ralsei/self-lace/CAD/Board/selflace.sch

## EAGLE design CAD/Board/selflace.sch (2019-05-23)

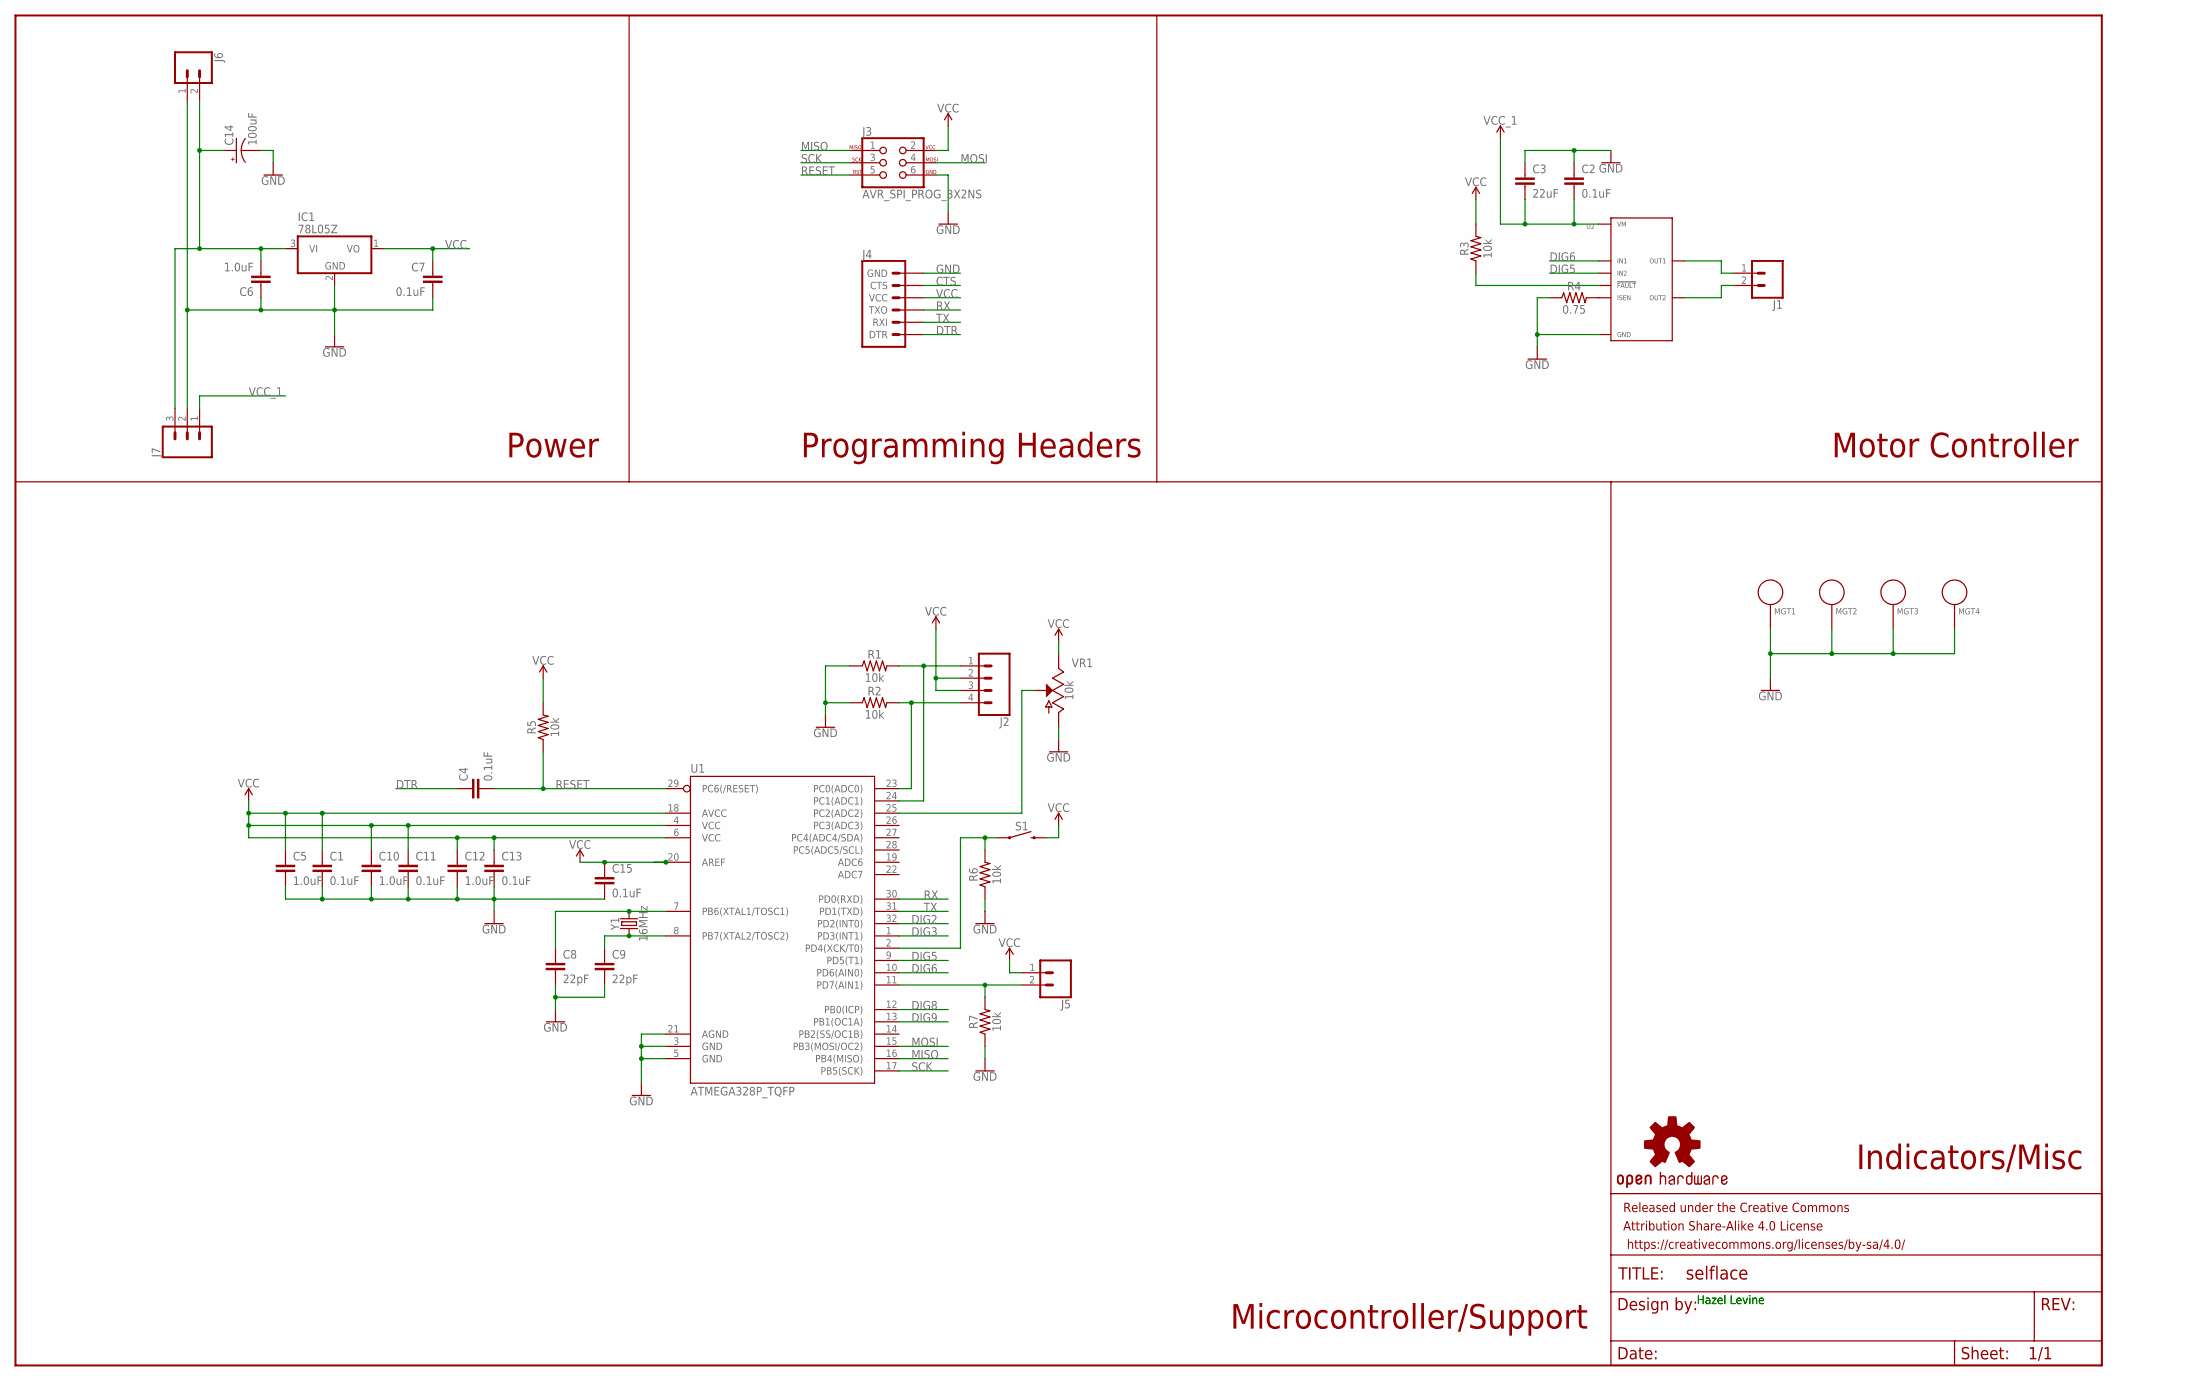
[picture p19: schematic selflace.sch]

Parts:
C1, C2, C4, C7, C11, C13, C15: 0.1uF; 0603
C3: 22uF; 0805
C5, C6, C10, C12: 1.0uF; 0603
C8, C9: 22pF; 0603
C14: 100uF; NIC_10X10.5_CAP
FRAME1: FRAME-LEDGER; CREATIVE_COMMONS
IC1: 78L05Z; TO92
J1, J5: CONN_02; 1X02
J2: CONN_04; 1X04
J3: AVR_SPI_PROG_3X2NS; 2X3-NS
J4: 6_PIN_SERIAL_TARGETSILK; 6_PIN_SERIAL_TARGET_SIDE_W_SILK
J6: CONN_02JST-PTH-2; JST-2-PTH
J7: CONN_03; 1X03
LOGO1: OSHW-LOGOM; OSHW-LOGO-M
MGT1, MGT2, MGT3, MGT4: BEAGLEBONEBLACK_MOUNTING_HOLE
R1, R2, R3, R5, R6, R7: 10k; 0603
R4: 0.75; 0805
S1: MOMENTARY-SWITCH-SPST-PTH-6.0MM; TACTILE_SWITCH_PTH_6.0MM
U1: ATMEGA328P_TQFP; TQFP32-08
U2: DRV8872DDARQ1; DRV8872_HSOP-8
VR1: 10k; POT-PTH-ALPS
Y1: 16MHz; HC49US

Connections:
CTS: J4.P$5 (CTS)
DIG2: U1.32 (PD2(INT0))
DIG3: U1.1 (PD3(INT1))
DIG5: U1.9 (PD5(T1)), U2.P$2 (IN2)
DIG6: U1.10 (PD6(AIN0)), U2.P$3 (IN1)
DIG8: U1.12 (PB0(ICP))
DIG9: U1.13 (PB1(OC1A))
DTR: C4.1, J4.P$1 (DTR)
GND: C1.2, C2.1, C3.1, C5.2, C6.1, C7.2, C8.2, C9.2, C10.2, C11.2, C12.2, C13.2, C14.-, C15.2, IC1.2 (GND), J3.6, J4.P$6 (GND), J6.1, J7.2, MGT1.P$1, MGT2.P$1, MGT3.P$1, MGT4.P$1, R1.1, R2.1, R4.1, R6.1, R7.1, U1.3 (GND), U1.5 (GND), U1.21 (AGND), U2.P$1 (GND), VR1.P$3 (A)
MISO: J3.1, U1.16 (PB4(MISO))
MOSI: J3.4, U1.15 (PB3(MOSI/OC2))
unnamed: R6.2, S1.1, U1.2 (PD4(XCK/T0))
unnamed: J5.2, R7.2, U1.11 (PD7(AIN1))
unnamed: R3.1, U2.P$4 (!FAULT)
unnamed: J1.1, U2.P$6 (OUT1)
unnamed: J1.2, U2.P$8 (OUT2)
unnamed: U1.25 (PC2(ADC2)), VR1.P$2 (S)
unnamed: C8.1, U1.7 (PB6(XTAL1/TOSC1)), Y1.2
unnamed: R4.2, U2.P$7 (ISEN)
unnamed: J2.4, R2.2, U1.23 (PC0(ADC0))
unnamed: J2.1, R1.2, U1.24 (PC1(ADC1))
unnamed: C9.1, U1.8 (PB7(XTAL2/TOSC2)), Y1.1
unnamed: C6.2, C14.+, IC1.3 (VI), J6.2, J7.3
RESET: C4.2, J3.5, R5.1, U1.29 (PC6(/RESET))
RX: J4.P$2 (TXO), U1.30 (PD0(RXD))
SCK: J3.3, U1.17 (PB5(SCK))
TX: J4.P$3 (RXI), U1.31 (PD1(TXD))
VCC: C1.1, C5.1, C7.1, C10.1, C11.1, C12.1, C13.1, C15.1, IC1.1 (VO), J2.2, J2.3, J3.2, J4.P$4 (VCC), J5.1, R3.2, R5.2, S1.3 (2), U1.4 (VCC), U1.6 (VCC), U1.18 (AVCC), U1.20 (AREF), VR1.P$1 (E)
VCC_1: C2.2, C3.2, J7.1, U2.P$5 (VM)

Notes on the sheet:
Hazel Levine
Power
Microcontroller/Support
Programming Headers
Motor Controller
Indicators/Misc
